Yuri-Lima/Link-House/Images/6.jpg

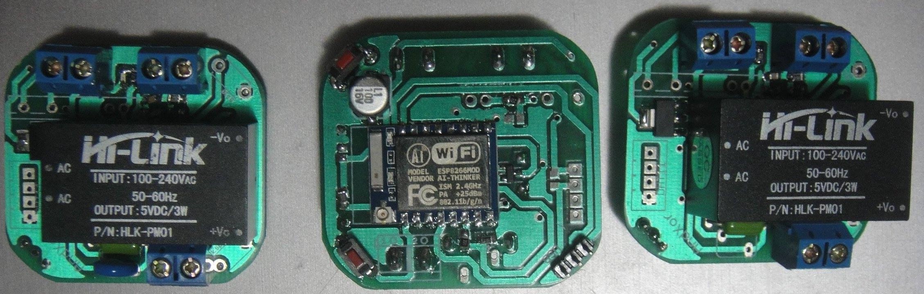
Images/6.jpg
