Yuri-Lima/Link-House/Images/20160217_213153.jpg

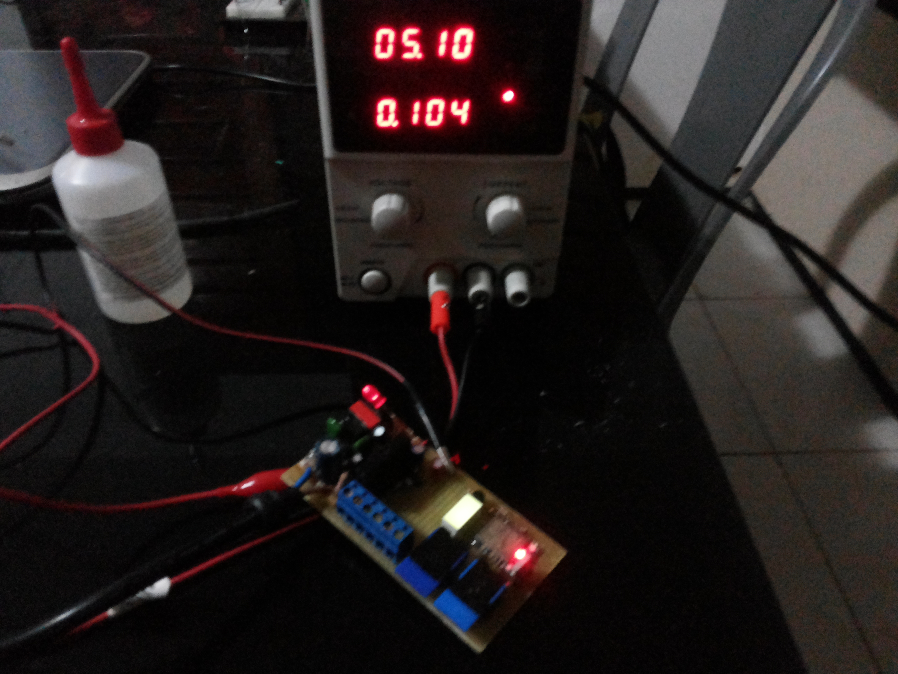
Images/20160217_213153.jpg
