Yuri-Lima/Link-House/Images/20160217_213203.jpg

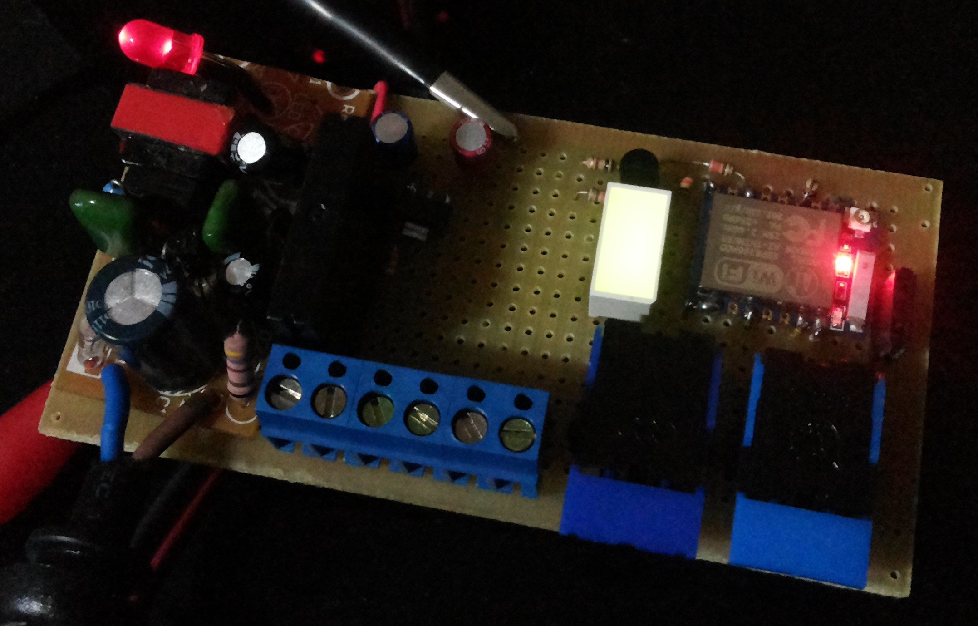
Images/20160217_213203.jpg
