Yuri-Lima/Link-House/Images/20160218_202940.jpg

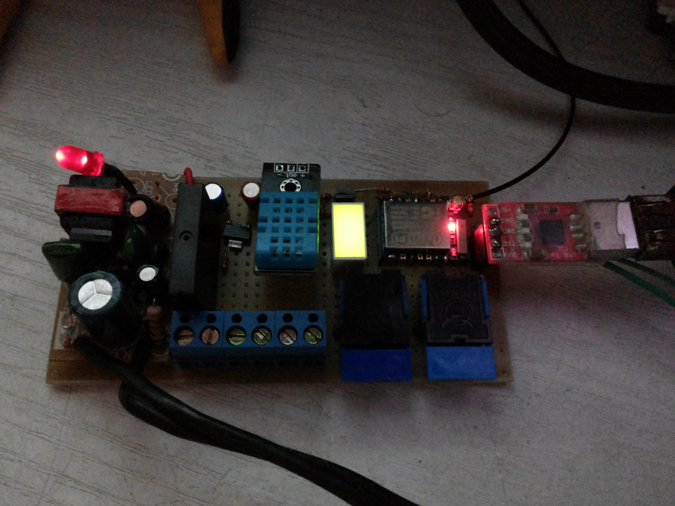
Images/20160218_202940.jpg
