Yuri-Lima/Link-House/Images/20160222_224902.jpg

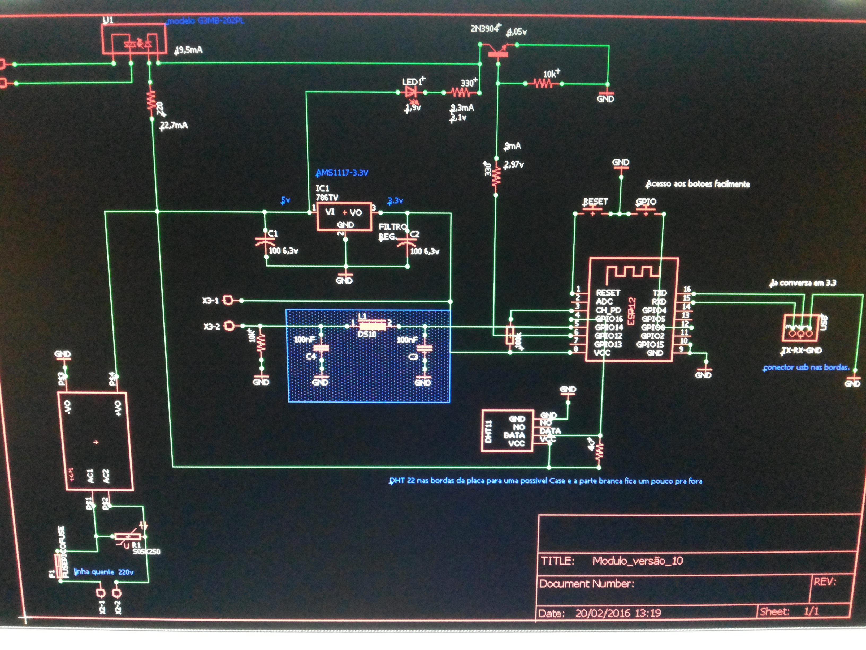
Images/20160222_224902.jpg
