Yuri-Lima/Link-House/Images/20160222_224914.jpg

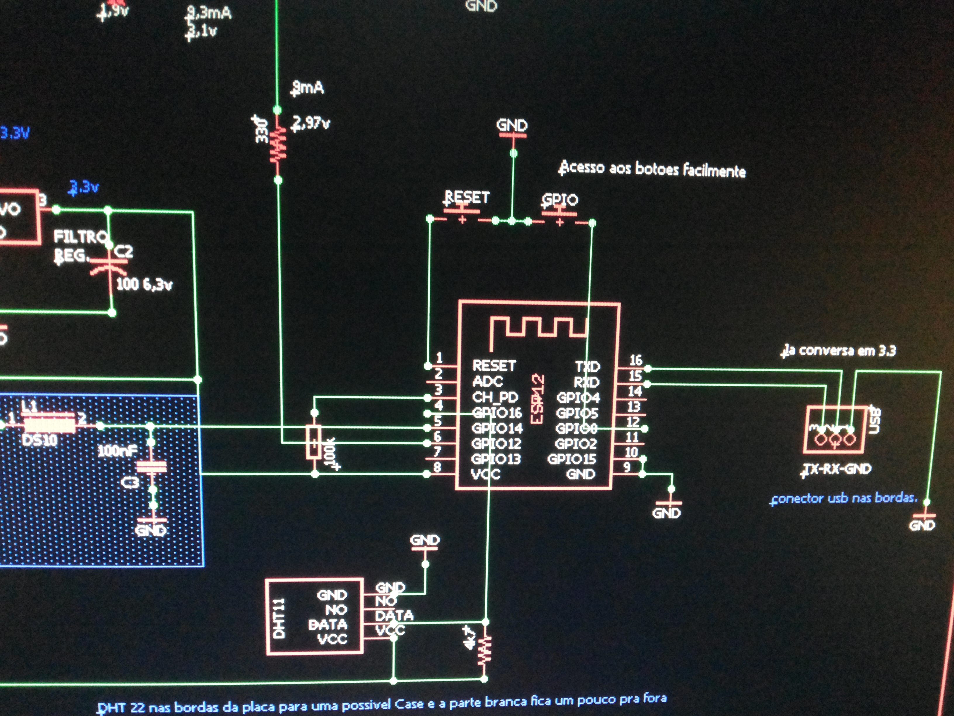
Images/20160222_224914.jpg
