Yuri-Lima/Link-House/Images/20160317_144207.jpg

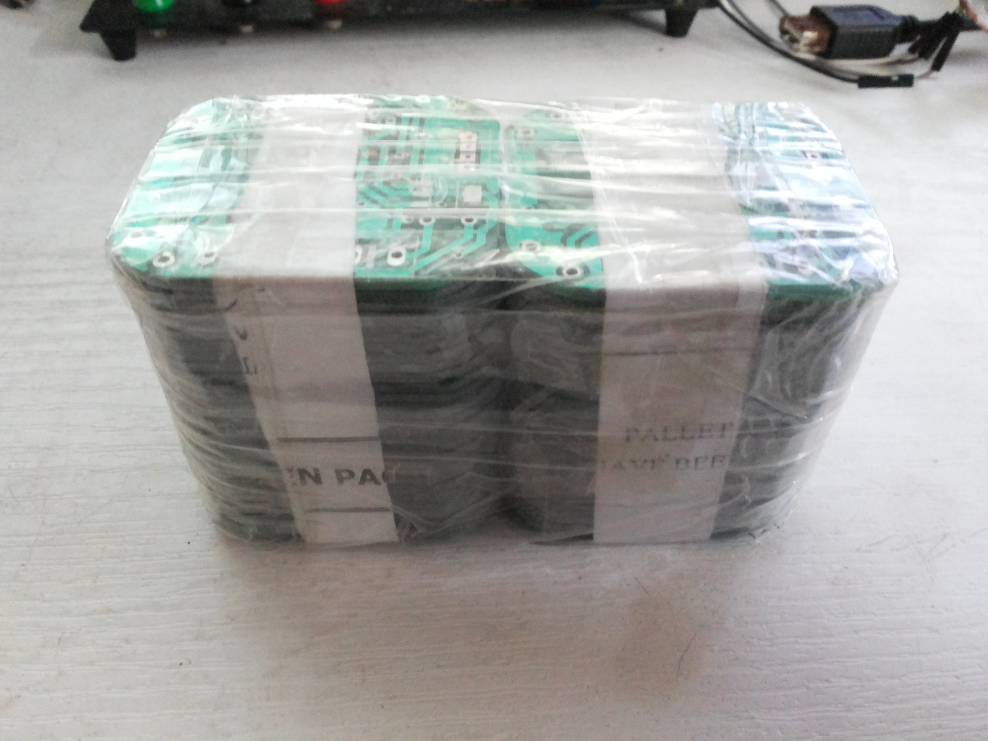
Images/20160317_144207.jpg
