Yuri-Lima/Link-House/Images/20160317_144213.jpg

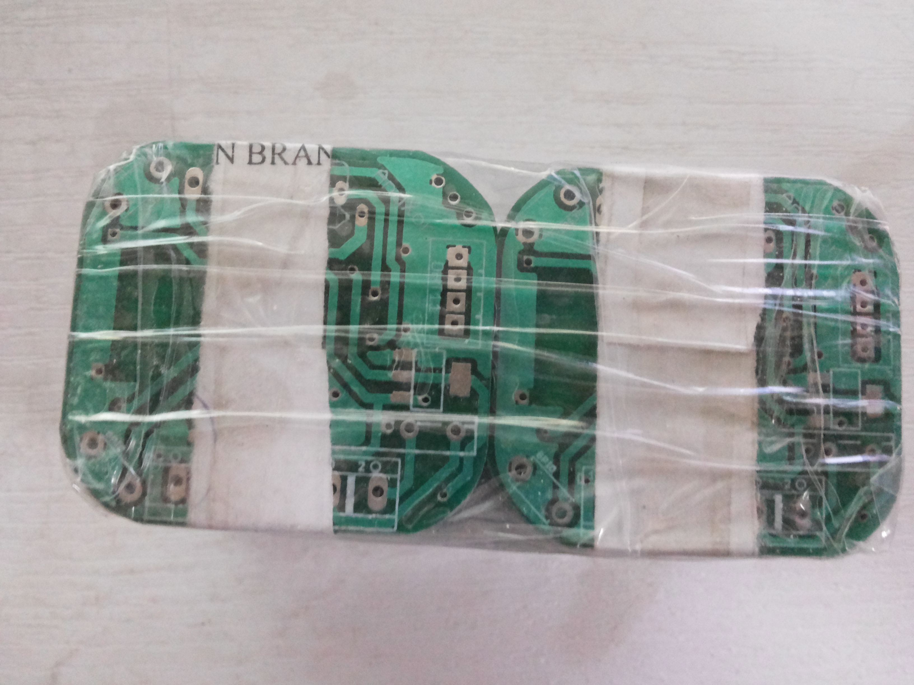
Images/20160317_144213.jpg
