Yuri-Lima/Link-House/Images/20160317_224306.jpg

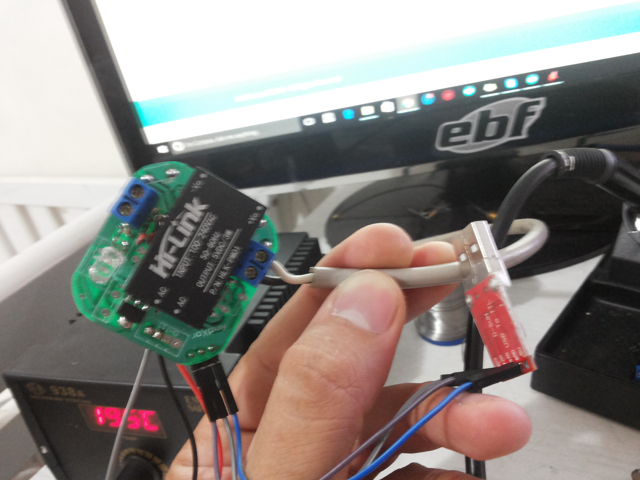
Images/20160317_224306.jpg
