Yuri-Lima/Link-House/OLD Things/Case_Homefi/Componentes_Placa/Pinos.SLDPRT

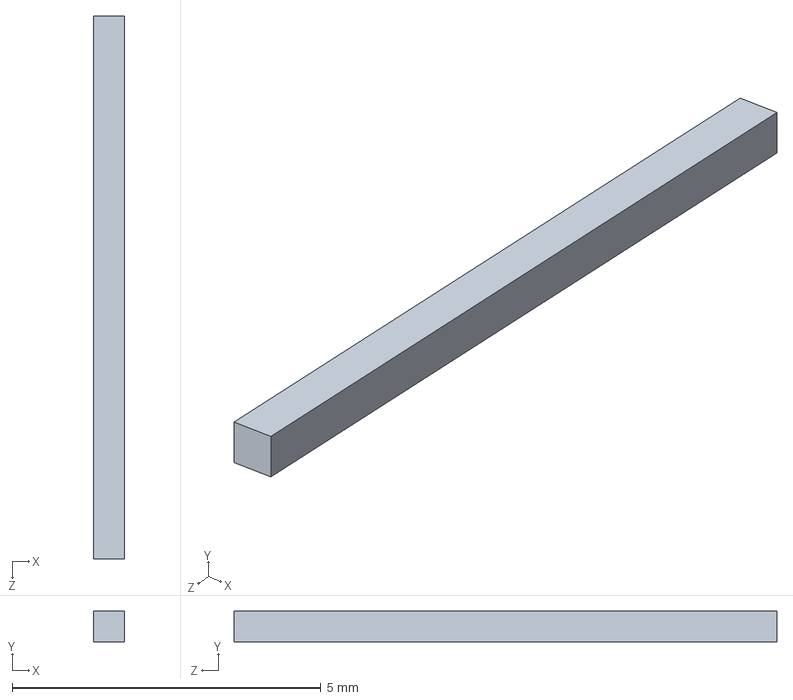
[picture p32: CAD file, 2020-07-04, an earlier design]
OLD Things/Case_Homefi/Componentes_Placa/Pinos.SLDPRT
0.5 x 0.5 x 8.80 mm
