Yuri-Lima/Link-House/OLD Things/Case_Homefi/Case_Homefi.SLDPRT

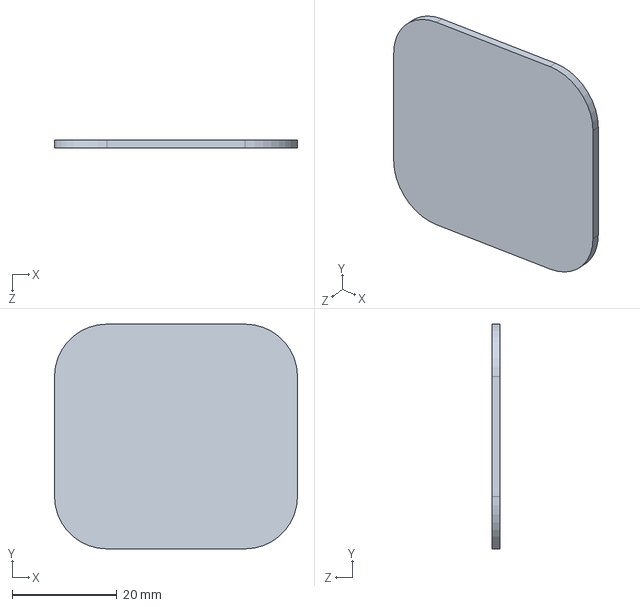
[picture p33: CAD file, 2020-07-04, an earlier design]
OLD Things/Case_Homefi/Case_Homefi.SLDPRT
46.5 x 43.0 x 1.60 mm
