Yuri-Lima/Link-House/OLD Things/Case_Homefi/Componentes_Placa/antenna-9.snapshot.2/Wire_Top_Radio_Antenna.SLDPRT

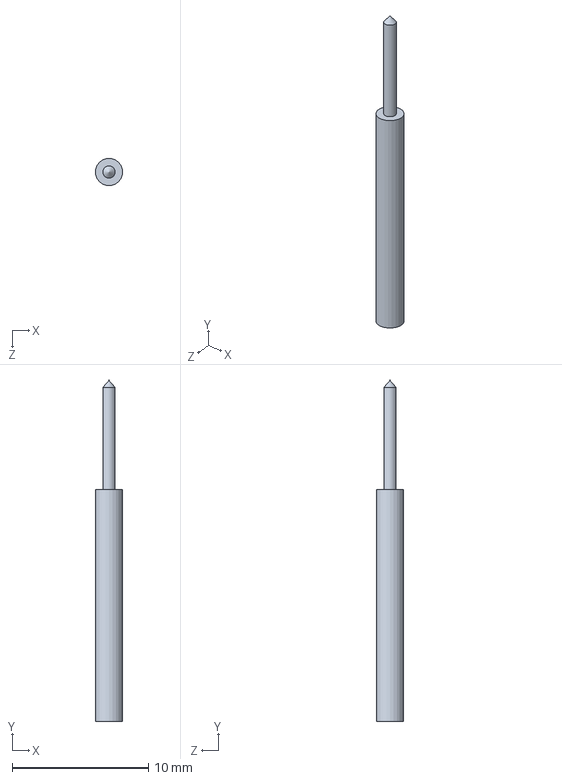
[picture p34: CAD file, 2020-07-04, an earlier design]
OLD Things/Case_Homefi/Componentes_Placa/antenna-9.snapshot.2/Wire_Top_Radio_Antenna.SLDPRT
2.00 x 25.0 x 2.00 mm
